Vinagre/phillipsTotalface-alternative/docs/ficha-encaixe.jpg

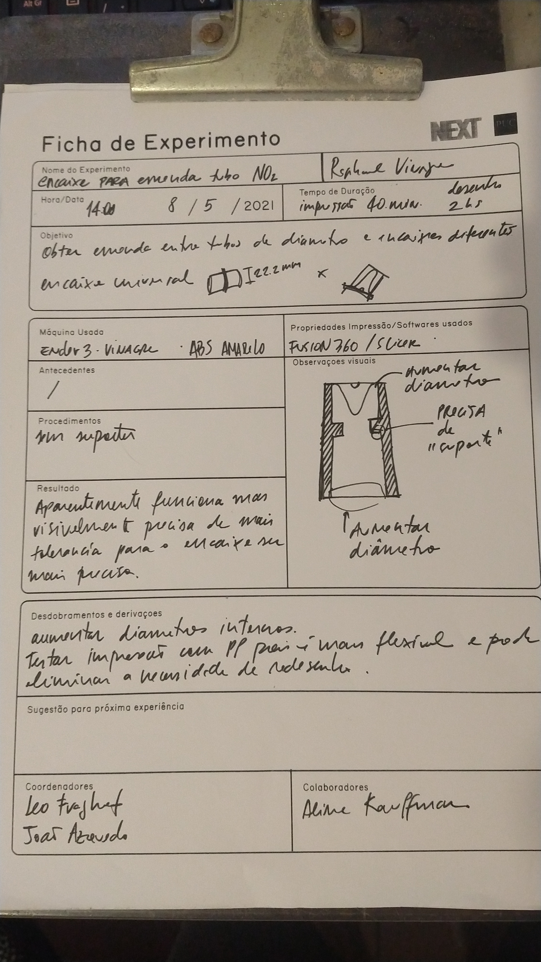
docs/ficha-encaixe.jpg
