Vinagre/phillipsTotalface-alternative/images/deliver.jpeg

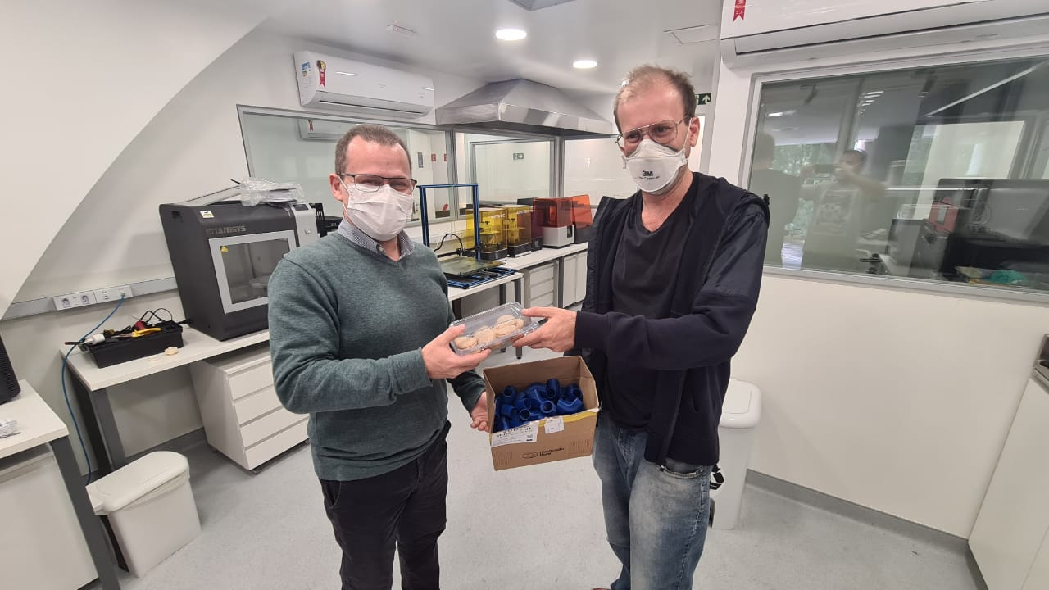
images/deliver.jpeg
