Vinagre/phillipsTotalface-alternative/images/encaixes (1).jpeg

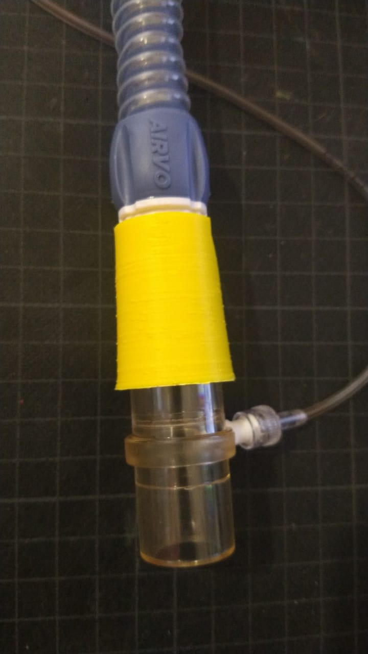
images/encaixes (1).jpeg
