Vinagre/phillipsTotalface-alternative/images/encaixes (2).jpeg

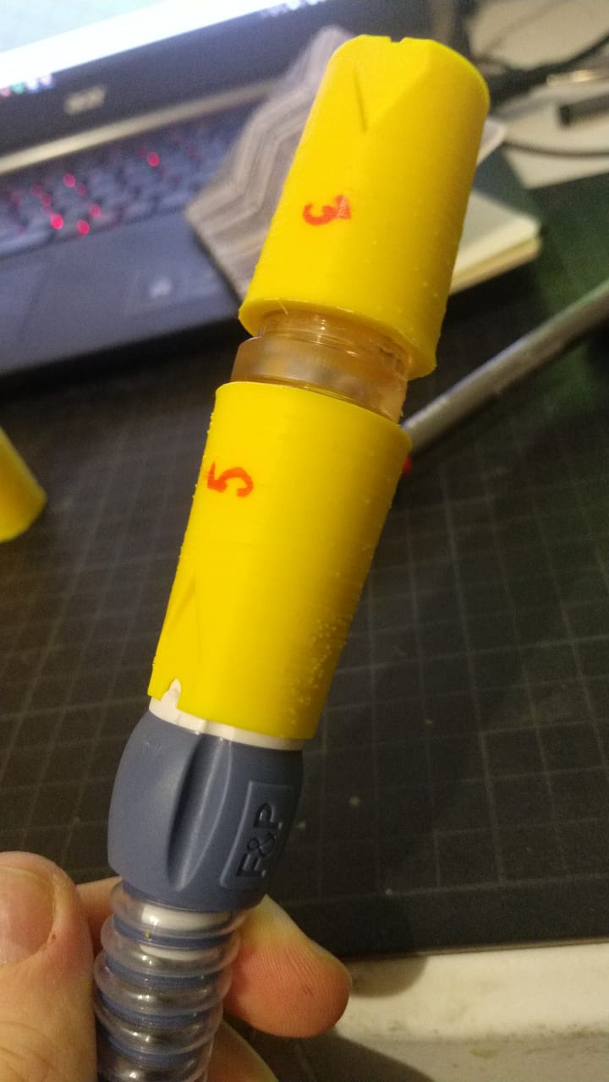
images/encaixes (2).jpeg
