Vinagre/phillipsTotalface-alternative/images/mask-detail.jpg

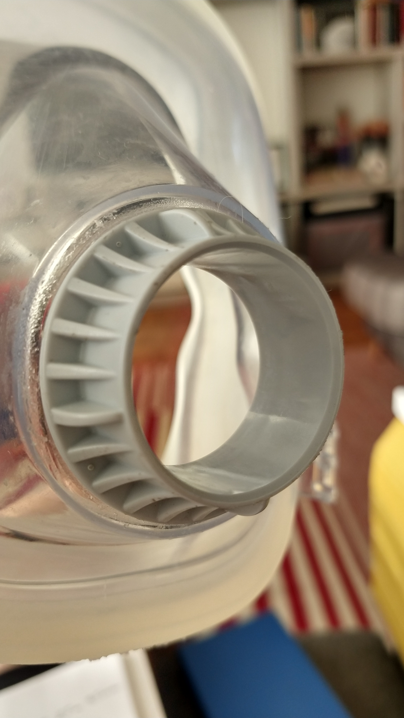
images/mask-detail.jpg
