Vinagre/phillipsTotalface-alternative/images/variations.jpg

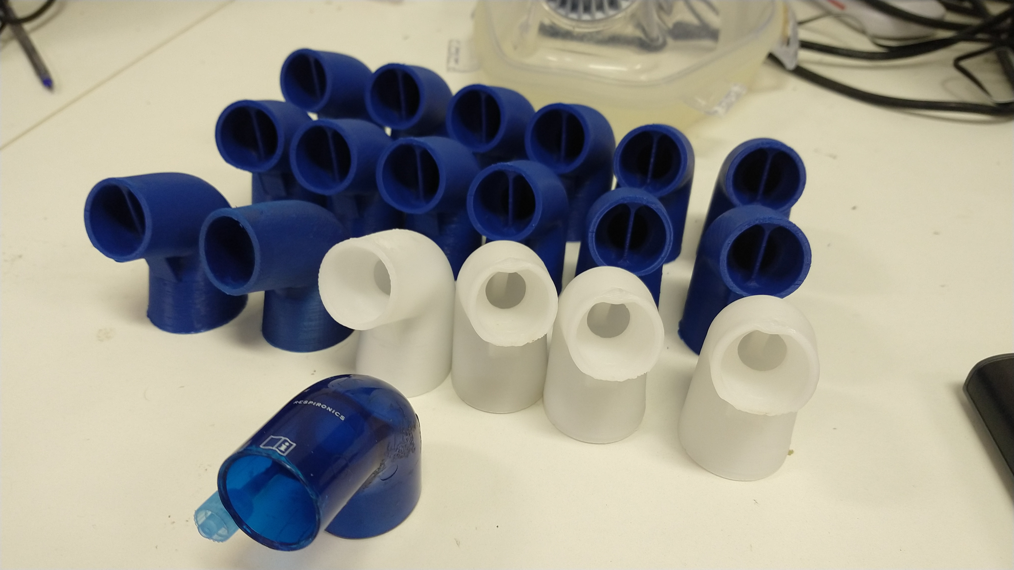
images/variations.jpg
