Vinagre/phillipsTotalface-alternative/images/test-setupo-01.jpeg

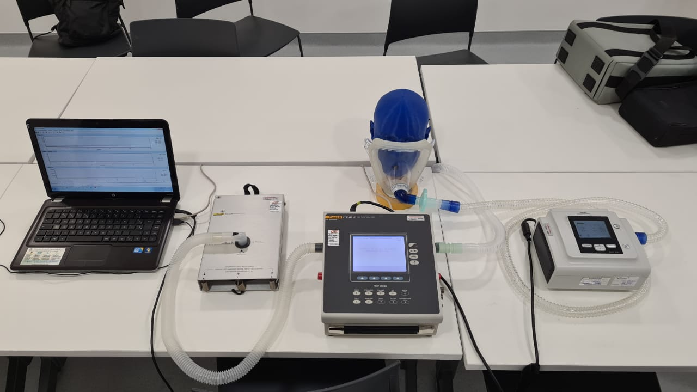
images/test-setupo-01.jpeg
